uvmaero/AERO_2022_2023_Code/Tutorials/Practice PCB/Practice PCB.kicad_pcb

## KiCad design Tutorials/Practice PCB/Practice PCB.kicad_pcb (2022-10-17, last stored version)

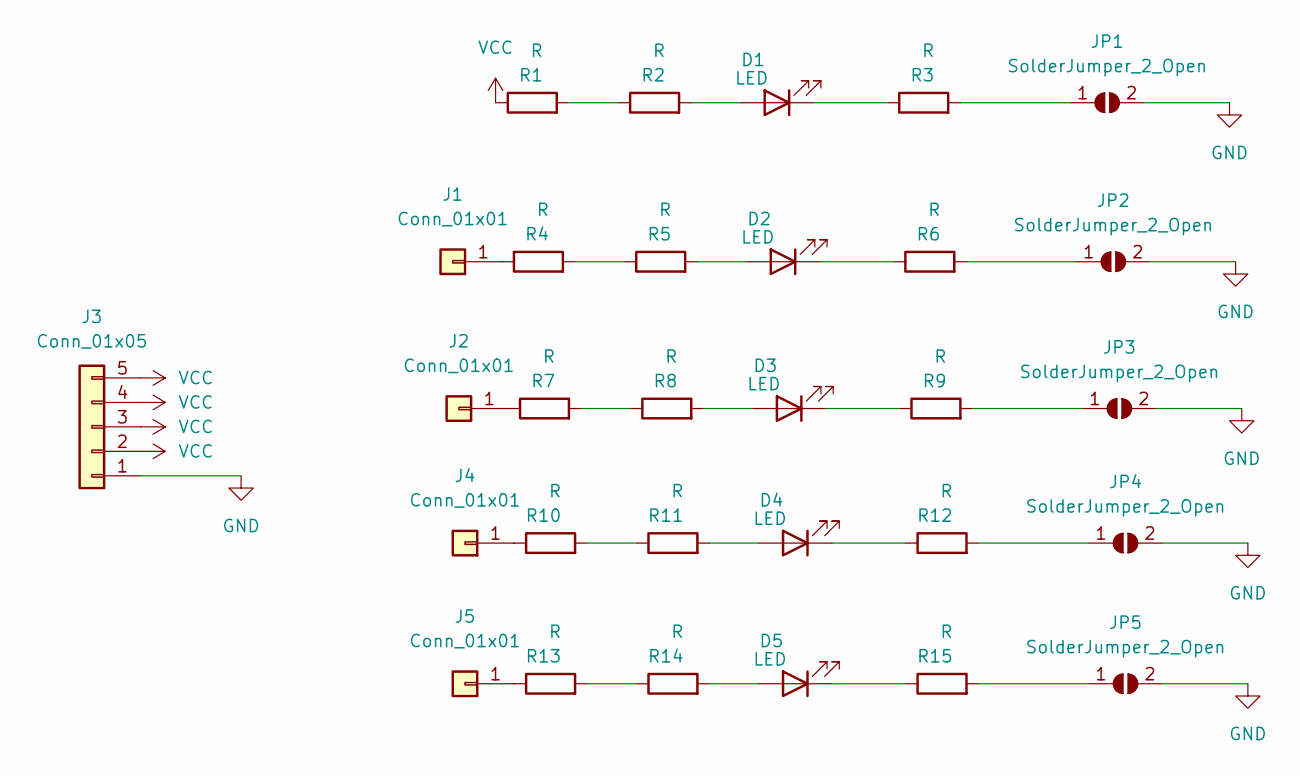
[picture p19: schematic Practice PCB.kicad_sch]

Parts:
D1, D2, D3, D4, D5: LED; LED_0603_1608Metric_Pad1.05x0.95mm_HandSolder
J1, J2, J4, J5: Conn_01x01; PinSocket_1x01_P2.00mm_Vertical
J3: Conn_01x05; SolderWire-1.5sqmm_1x05_P6mm_D1.7mm_OD3mm
JP1, JP3, JP5: SolderJumper_2_Open; SolderJumper-2_P1.3mm_Open_RoundedPad1.0x1.5mm
JP2, JP4: SolderJumper_2_Open; SolderJumper-2_P1.3mm_Open_Pad1.0x1.5mm
R1, R4, R7, R10, R13: R; R_Axial_DIN0411_L9.9mm_D3.6mm_P7.62mm_Vertical
R2, R5, R8, R11, R14: R; R_Axial_DIN0411_L9.9mm_D3.6mm_P12.70mm_Horizontal
R3, R6, R9, R12, R15: R; R_0603_1608Metric_Pad0.98x0.95mm_HandSolder

Connections:
GND: J3.1, JP1.2 (B), JP2.2 (B), JP3.2 (B), JP4.2 (B), JP5.2 (B)
unnamed: D1.1 (K), R3.1
unnamed: D1.2 (A), R2.2
unnamed: D2.1 (K), R6.1
unnamed: D2.2 (A), R5.2
unnamed: D3.1 (K), R9.1
unnamed: D3.2 (A), R8.2
unnamed: D4.1 (K), R12.1
unnamed: D4.2 (A), R11.2
unnamed: D5.1 (K), R15.1
unnamed: D5.2 (A), R14.2
unnamed: J1.1, R4.1
unnamed: J2.1, R7.1
unnamed: J4.1, R10.1
unnamed: J5.1, R13.1
unnamed: JP1.1 (A), R3.2
unnamed: JP2.1 (A), R6.2
unnamed: JP3.1 (A), R9.2
unnamed: JP4.1 (A), R12.2
unnamed: JP5.1 (A), R15.2
unnamed: R1.2, R2.1
unnamed: R4.2, R5.1
unnamed: R7.2, R8.1
unnamed: R10.2, R11.1
unnamed: R13.2, R14.1
VCC: J3.2, J3.3, J3.4, J3.5, R1.1

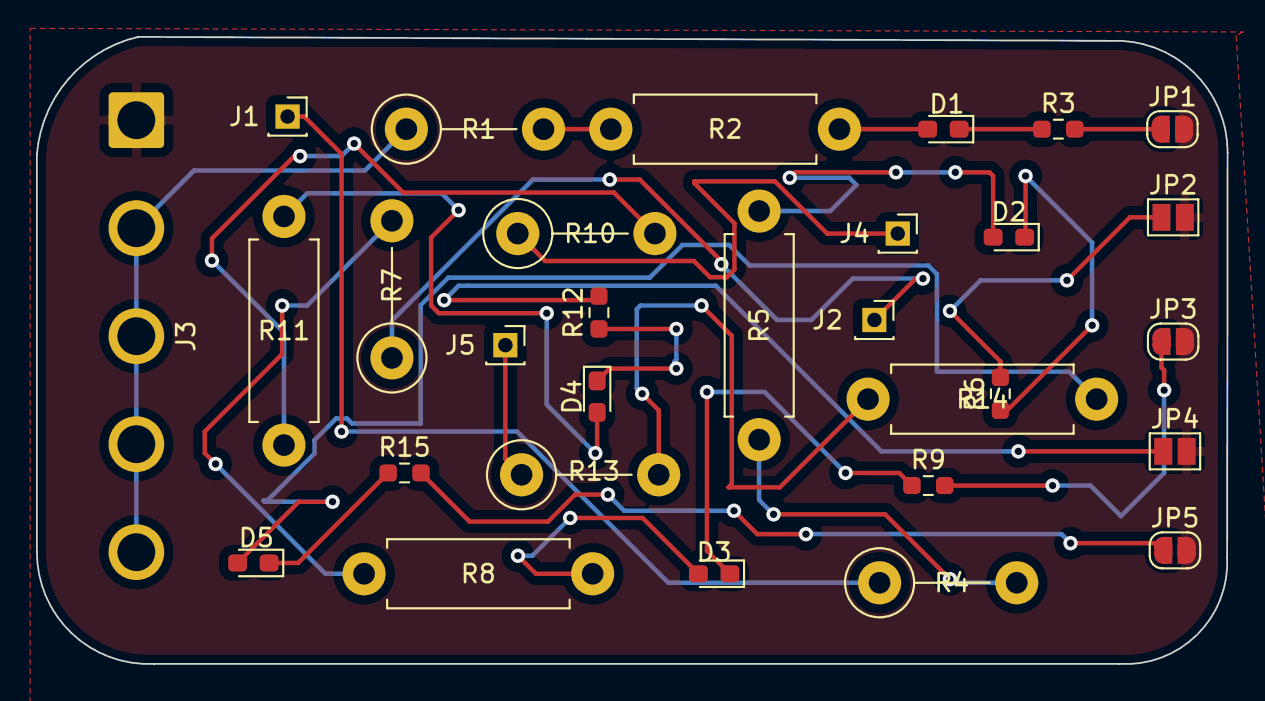
[picture p20: board Practice PCB.kicad_pcb from above]

Board: 2 copper layers, 66.2 x 34.8 mm, 30 parts (0 on the bottom side), 26 nets.
